arduino/Steelwonder/plastic parts (source)/OpenSCAD/includes/Base_cama.dxf

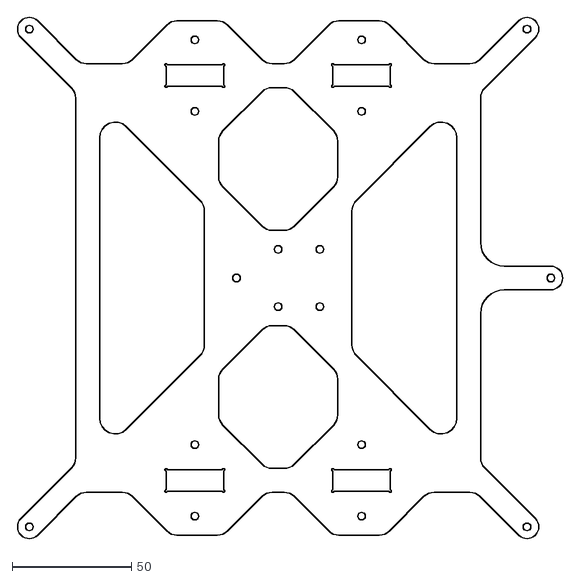
[picture p15: CAD file, 2014-10-17]
plastic parts (source)/OpenSCAD/includes/Base_cama.dxf
229.4 x 219.9
